legut2/Green-Box-Remotely-Controlled-Outlet/images/data_sent.png

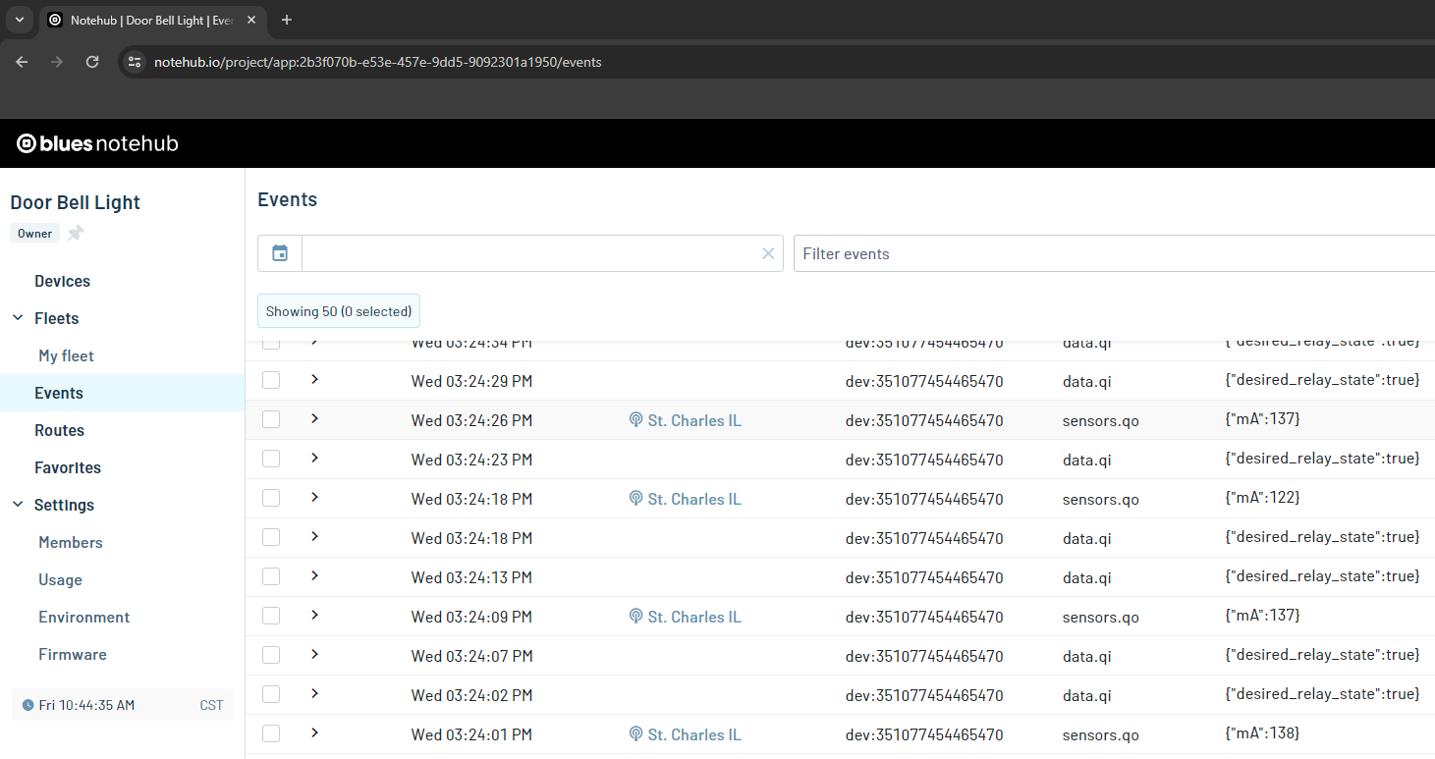
images/data_sent.png
