legut2/Green-Box-Remotely-Controlled-Outlet/images/device id.png

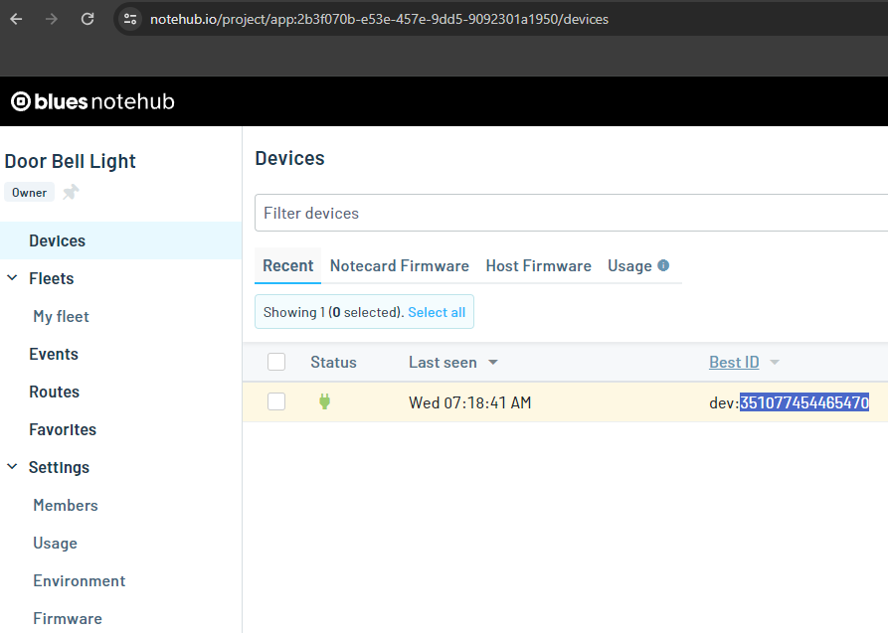
images/device id.png
