legut2/Green-Box-Remotely-Controlled-Outlet/images/generate programmatic access.png

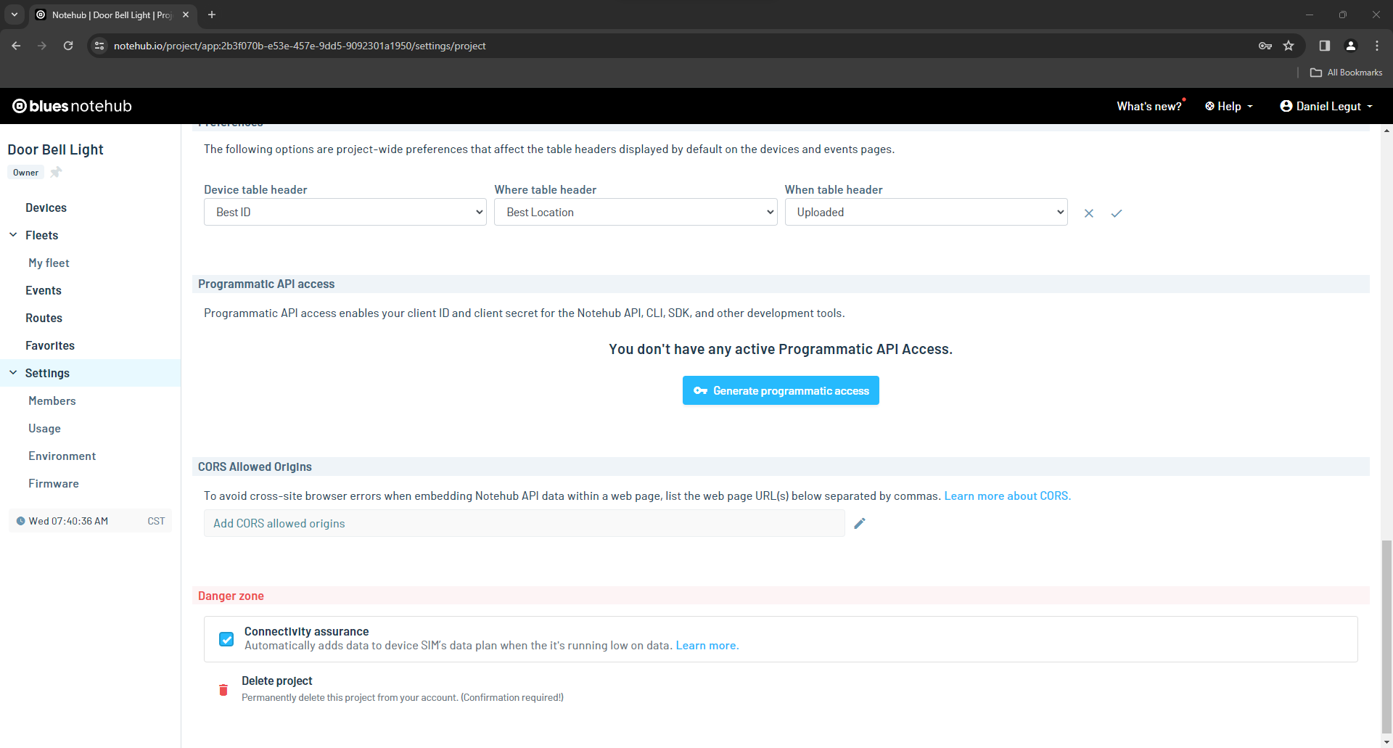
images/generate programmatic access.png
