legut2/Green-Box-Remotely-Controlled-Outlet/images/project id at top of settings.png

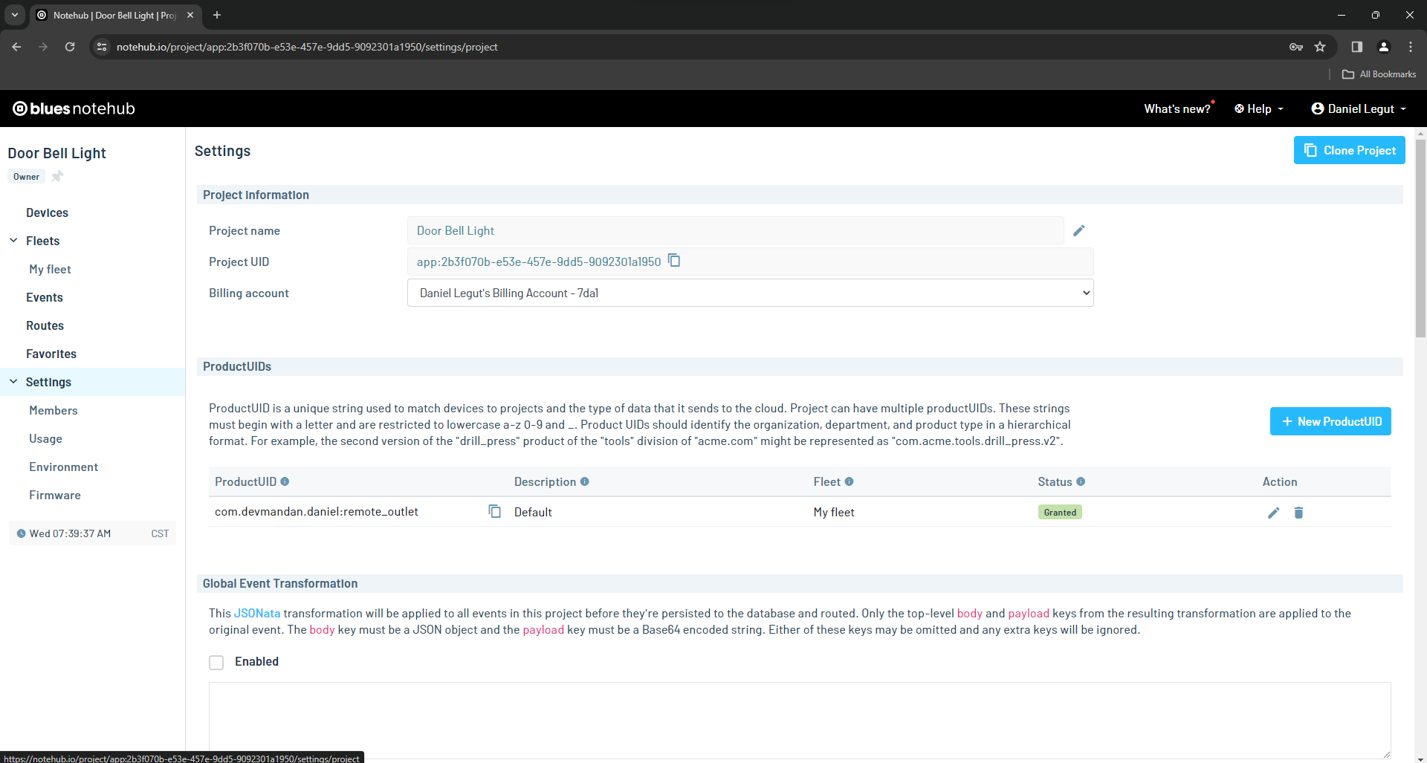
images/project id at top of settings.png
