legut2/Green-Box-Remotely-Controlled-Outlet/images/receive commands.png

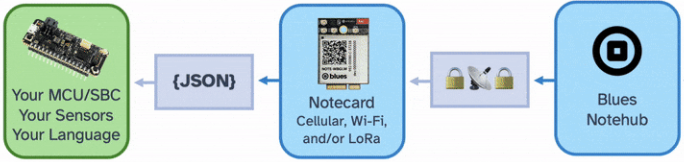
images/receive commands.png
