legut2/Green-Box-Remotely-Controlled-Outlet/images/settings1.png

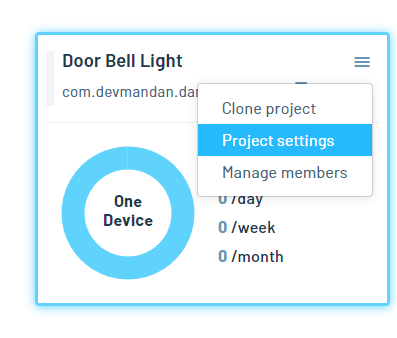
images/settings1.png
